protieusz/StarShip-Centurion/sscenturion/keymaps/default/keymap.c

/*
Copyright 2022 aki27

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
You should have received a copy of the GNU General Public License
along with this program.  If not, see <http://www.gnu.org/licenses/>.
*/

#include QMK_KEYBOARD_H

enum combo_events {
  COMBO_DEL,
  COMBO_ESC,
  //COMBO_CTRL,
  //COMBO_ALT,
  COMBO_LENGTH
};
uint16_t COMBO_LEN = COMBO_LENGTH;

const uint16_t PROGMEM combo_del[] = {KC_Y, KC_H, COMBO_END};
const uint16_t PROGMEM combo_esc[] = {KC_T, KC_G, COMBO_END};
//const uint16_t PROGMEM combo_ctrl[] = {KC_Q, KC_W, COMBO_END};
//const uint16_t PROGMEM combo_alt[] = {KC_O, KC_P, COMBO_END};

combo_t key_combos[] = {
  [COMBO_DEL] = COMBO(combo_del, KC_DEL),
  [COMBO_ESC] = COMBO(combo_esc, KC_ESC),
  //[COMBO_CTRL] = COMBO(combo_ctrl, KC_LCTL),
  //[COMBO_ALT] = COMBO(combo_alt, KC_RALT),

};

layer_state_t layer_state_set_user(layer_state_t state) {
    return update_tri_layer_state(state, 1, 2, 3);
} 

enum layer_names {
  _BASE,
  _FN1,
  _FN2,
  _FN3
};

const uint16_t PROGMEM keymaps[][MATRIX_ROWS][MATRIX_COLS] = {
    
    [_BASE] = LAYOUT(
        KC_Q,         KC_W, KC_E,    KC_R,    KC_T,                      KC_MS_BTN1,             KC_Y,          KC_U,          KC_I,     KC_O,   KC_P,
        KC_A,         KC_S, KC_D,    KC_F,    KC_G,                      SCRL_MO,                KC_H,          KC_J,          KC_K,     KC_L,   KC_SCLN,
        LSFT_T(KC_Z), KC_X, KC_C,    KC_V,    KC_B,                      KC_MS_BTN2,             KC_N,          KC_M,          KC_COMMA, KC_DOT, RSFT_T(KC_SLSH),
                            KC_LGUI, KC_LCTL, LT(1,KC_BSPC),                                     LT(2,KC_SPC),  (KC_ENT),      KC_LALT                        
    ),
    [_FN1] = LAYOUT(
        KC_1,    KC_2,    KC_3,    KC_4,    KC_5,                  _______,                   KC_6,     KC_7,    KC_8,    KC_9,    KC_0,
        KC_TAB,  _______, _______, _______, _______,               _______,                   KC_MINS,  KC_EQL,  KC_LBRC, KC_RBRC, KC_QUOT,
        _______, _______, KC_MUTE, KC_VOLD, KC_VOLU,               _______,                   KC_TILD,  KC_GRV,  _______, _______, KC_BSLS,
                          _______, _______, _______,                                          _______, _______,  _______                   
    ),
    [_FN2] = LAYOUT(
        KC_EXLM, KC_AT,   KC_HASH, KC_DLR,  KC_PERC,                 _______,                   KC_CIRC, KC_AMPR, KC_ASTR, KC_LPRN, KC_RPRN,
        RGB_VAI,  RGB_SAI,    RGB_HUI,    RGB_SPI,   RGB_MOD,        _______,                   RGB_TOG,  _______,  _______, _______, _______, 
        RGB_VAD,  RGB_SAD,    RGB_HUD,    RGB_SPD,   RGB_RMOD,       _______,                   _______,  _______, _______, _______, _______,
                                    _______, _______, _______,                                  _______, _______,  _______                  
    ),
    [_FN3] = LAYOUT(
        _______, KC_UP, _______, _______, _______,               _______,                    KC_F1,   KC_F2,   KC_F3,   KC_F4,   KC_PSCR,
        KC_LEFT, KC_DOWN, KC_RIGHT, _______, _______,            _______,                    KC_F5,   KC_F6,   KC_F7,   KC_F8,   KC_F9,
        _______, _______, ROT_L15, ROT_R15, CPI_SW,              _______,                    KC_F10,  KC_F11,  KC_F12,  _______, _______,
                         _______, _______, _______,                                          _______, _______,  _______                   
    )
};

//bool encoder_update_user(uint8_t index, bool clockwise) {
    //if (index == 0) {
        //if (clockwise) {
            //tap_code(KC_VOLD);
            //tap_code(KC_MS_WH_UP);
        //} else {
            //tap_code(KC_VOLU);
            //tap_code(KC_MS_WH_DOWN);
        //}
    //}
    //return true;
//}

/* My Encoder Codes */
//#if defined(ENCODER_MAP_ENABLE)
//const uint16_t PROGMEM encoder_map[][NUM_ENCODERS][2] = {
    //[0] =  { ENCODER_CCW_CW(KC_MS_WH_UP, KC_MS_WH_DOWN)  },
    //[1] =  { ENCODER_CCW_CW(KC_MS_WH_LEFT, KC_MS_WH_RIGHT)  },
    //[2] =  { ENCODER_CCW_CW(KC_PGUP, KC_PGDN)  },
    //[3] =  { ENCODER_CCW_CW(KC_VOLD, KC_VOLU)  } 
    //[4] =  { ENCODER_CCW_CW(XXXXXXX, XXXXXXX) }
//};
//#endif

//keyevent_t encoder1_ccw = {
    //.key = (keypos_t){.row = 3, .col = 0},
    //.pressed = false
//};

//keyevent_t encoder1_cw = {
    //.key = (keypos_t){.row = 3, .col = 9},
    //.pressed = false
//};

//bool encoder_update_user(uint8_t index, bool clockwise) {
    //if (index == 0) { /* First encoder */
        //if (clockwise) {
            //encoder1_cw.pressed = true;
            //encoder1_cw.time = (timer_read() | 1);
            //action_exec(encoder1_cw);
        //} else {
            //encoder1_ccw.pressed = true;
            //encoder1_ccw.time = (timer_read() | 1);
            //action_exec(encoder1_ccw);
        //}
    //}

    //return true;
//}

//void matrix_scan_user(void) {

    //if (IS_PRESSED(encoder1_ccw)) {
        //encoder1_ccw.pressed = false;
        //encoder1_ccw.time = (timer_read() | 1);
        //action_exec(encoder1_ccw);
    //}

    //if (IS_PRESSED(encoder1_cw)) {
        //encoder1_cw.pressed = false;
        //encoder1_cw.time = (timer_read() | 1);
        //action_exec(encoder1_cw);
    //}

//}
